ThorSc/RFIDwisp-ESP32-dev/wt32sc01plus/src/settings.h

#pragma once
#include <Arduino.h>

// The subset of AppSettings from the Flutter app that this firmware needs.
// WiFi credentials are not stored here - WiFiManager keeps those in its own
// NVS namespace.
struct AppSettings {
  String spoolmanAddress = ""; // e.g. http://spoolman.local:7912
  bool useSpoolman = false;
  uint8_t sleepMinutes = 10; // screen sleep timeout, 0-60 minutes, 0 = never
  bool checkForUpdates = true; // look for a new firmware version at startup
  String otaPassword = ""; // OTA update password, empty = no auth required

  void load();
  void save() const;
};

extern AppSettings settings;
