ThorSc/RFIDwisp-ESP32-dev/wt32sc01plus/src/ui.h

#pragma once
#include "qidi_tag.h"
#include "spoolman_client.h"
#include <vector>

// Called once at startup, after displaySetup().
void uiInit();

// Fills the edit screen's fields from a spool just read off a tag and shows
// that screen. If a cached Spoolman spool matches spool.spoolNumber, the
// Spool selector is pointed at it instead of "New spool".
void uiShowSpool(const FilamentSpool &spool);

// Shows the edit screen for writing a new tag (blank fields, "New spool"
// selected). Called by main.cpp's handleWriteScreenOpened after refreshing
// the Spoolman caches (if Spoolman is active).
void uiShowEditScreenForWrite();

// Whether the edit screen currently shows the Spoolman-integrated fields
// (Spool selector + Spoolman vendor) instead of the plain QIDI vendor +
// manual spool number fields.
void uiSetSpoolmanMode(bool active);

// The cached Spoolman vendors/spools/filaments to show in the edit screen's
// dropdowns (Spool, Spoolman vendor, and Filament - the last one lets a new
// spool's Material/Colour/Vendor be prefilled from an existing filament,
// mirroring rfid_tag_panel.dart's second dropdown).
void uiSetSpoolmanLists(const std::vector<SpoolmanVendor> &vendors,
                        const std::vector<SpoolmanSpool> &spools,
                        const std::vector<SpoolmanFilament> &filaments);

// True if "New spool" is selected on the edit screen (Spoolman mode only).
bool uiIsNewSpoolSelected();

// The id of the Spoolman spool selected on the edit screen; -1 if "New
// spool" is selected or Spoolman mode is off.
int uiSelectedExistingSpoolId();

// The Spoolman filament picked for a new spool (its material, colour and
// vendor are then fixed); -1 if none is picked.
int uiSelectedFilamentId();

// The Spoolman vendor id chosen for a new spool (Spoolman mode, "New spool"
// selected); -1 if none of the cached vendors is selected.
int uiSelectedSpoolmanVendorId();

// Updates the status line on the main screen.
void uiSetStatus(const char *text);

// Updates the Wi-Fi status line shown on the settings screen.
void uiSetWifiStatus(const char *text);

// The firmware update row of the settings screen: [status] is the line under
// the switches, [buttonText] the label of the button next to them (it checks
// for an update, or installs the one that was found).
void uiSetUpdateState(const char *status, const char *buttonText);

// Asks the user whether to install the firmware [version] now (modal dialog).
// "Install" ends up in main.cpp's handleInstallUpdateRequested().
void uiShowUpdatePrompt(const char *version);

// A full-screen "please wait" with [text] and, if [percent] is 0..100, a
// progress bar; blocks all input until uiHideBusy(). Call displayLoop()
// afterwards to make it appear while the caller keeps working.
void uiShowBusy(const char *text, int percent = -1);
void uiHideBusy();


// Reads the edit screen's fields back into a spool, for writing to a tag.
FilamentSpool uiCurrentSpool();
